BoarderGamez/Meshing-the-lora/costs/Screenshot from 2025-12-03 13-57-01.png

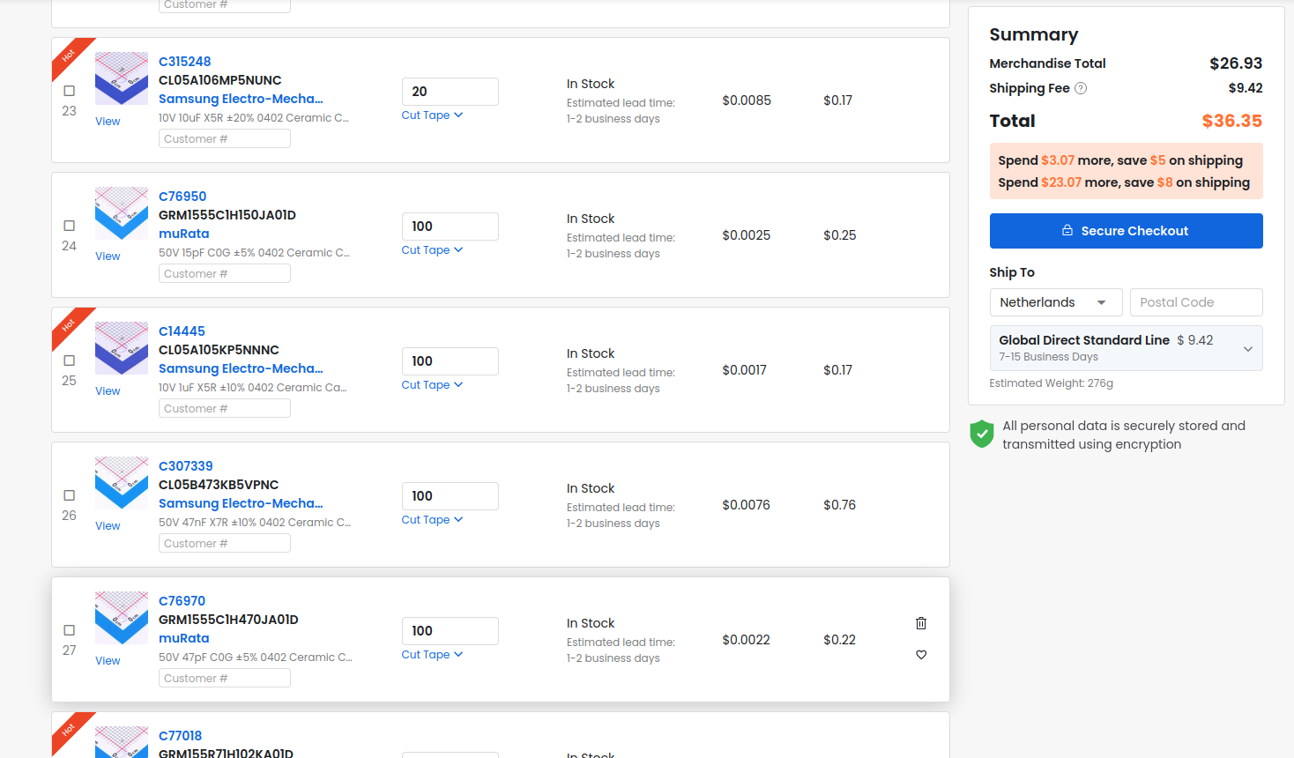
costs/Screenshot from 2025-12-03 13-57-01.png
