BoarderGamez/Meshing-the-lora/costs/Screenshot from 2025-12-03 14-11-08.png

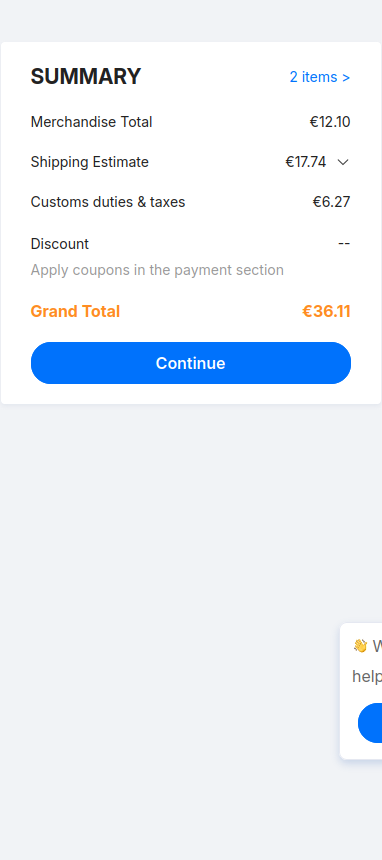
costs/Screenshot from 2025-12-03 14-11-08.png
